GM4AJK/gps-staff/firmware/Nucleo-F767ZI/openspec/changes/bno085-int-edge-flag/specs/bno085-spi-bringup/spec.md

## MODIFIED Requirements

### Requirement: Wait for data-ready and read SHTP packet
`bno085_bringup()` SHALL pulse `RST` low for `BNO085_RESET_PULSE_MS` then
high twice in succession, waiting `BNO085_STARTUP_T1_MS` after each pulse
before doing anything else - per datasheet 6.5.3 "Startup timing", `INT` is
undefined for this period (`t1`, Internal Initialization) after `RST` is
released. A single reset pulse does not reliably bring the device up
following a power cycle; a second pulse is required.

After the second reset pulse and its `BNO085_STARTUP_T1_MS` wait,
`bno085_bringup()` SHALL wait (with a timeout of
`BNO085_INT_DEASSERT_TIMEOUT_MS`) for `INT` to read high (deasserted),
to allow the device's in-reset/booting period - during which it may
read or drive `INT` low for reasons unrelated to data-ready - to pass.
Immediately after this deassert wait (whether `INT` read high or the
deassert wait timed out), `bno085_bringup()` SHALL discard any
previously-latched `BNO085_INT` edge flag (`flag_get_BNO085_INT()`).
`bno085_bringup()` SHALL then wait for `INT` to become active, with a
timeout of `BNO085_INT_TIMEOUT_MS`. `INT` is considered active as soon
as either the `BNO085_INT` edge flag is set (a falling edge was latched
by `HAL_GPIO_EXTI_Callback()` at any point since it was discarded) or
the `INT` GPIO pin currently reads low - whichever is observed first. If
`INT` becomes active within the timeout, the driver SHALL assert `CS`
low, perform a single `BNO085_BRINGUP_BUF_SIZE`-byte full-duplex SPI
transfer (transmitting all-zero bytes), then release `CS` high. The
driver SHALL parse the first 4 received bytes as the SHTP header: a
16-bit length (LSB first, with the continuation bit masked off) into
`shtp_length`, followed by one byte each into `shtp_channel` and
`shtp_sequence`. The full received buffer SHALL be stored in the
handle.

#### Scenario: Two reset pulses are issued before waiting for data-ready
- **WHEN** `bno085_bringup()` is called
- **THEN** `RST` is pulsed low for `BNO085_RESET_PULSE_MS` then high, the
  driver waits `BNO085_STARTUP_T1_MS` without sampling `INT`, and this
  is repeated a second time before any `INT` polling begins

#### Scenario: Successful read populates the handle and returns HAL_OK
- **WHEN** `bno085_bringup()` is called, `INT` becomes active (edge
  latched or level low) within `BNO085_INT_TIMEOUT_MS` of the second
  `RST` release, and the SPI transfer succeeds
- **THEN** `bno085_bringup()` returns `HAL_OK`
- **AND** the handle's `shtp_length`, `shtp_channel`, and `shtp_sequence`
  fields reflect the first 4 bytes received
- **AND** the handle's raw receive buffer contains all
  `BNO085_BRINGUP_BUF_SIZE` bytes received over SPI

#### Scenario: A falling edge latched before the level-poll loop starts is not missed
- **WHEN** `bno085_bringup()` is called, the deassert wait completes (or
  times out), the `BNO085_INT` edge flag is discarded, `INT` briefly
  pulses low and back high (latching the flag via
  `HAL_GPIO_EXTI_Callback()`) before the level-poll loop begins, and the
  SPI transfer succeeds
- **THEN** `bno085_bringup()` returns `HAL_OK` without waiting for
  `BNO085_INT_TIMEOUT_MS`

#### Scenario: An edge latched during the in-reset/booting period is not mistaken for data-ready
- **WHEN** `bno085_bringup()` is called and `INT` reads/pulses low only
  during the `RST` pulse or the deassert wait (before the `BNO085_INT`
  edge flag is discarded), and then reads high for the remainder of the
  deassert wait
- **THEN** the latched edge from that period is discarded and does not
  cause `bno085_wait_int_low()` to return immediately
- **AND** `bno085_bringup()` waits for a genuine post-boot assertion of
  `INT` (edge or level) before performing the SPI transfer

#### Scenario: INT timeout returns an error without an SPI transaction
- **WHEN** `bno085_bringup()` is called and `INT` does not become active
  (no edge latched after the discard, and the level never reads low)
  within `BNO085_INT_TIMEOUT_MS` after the deassert wait completes
- **THEN** `bno085_bringup()` returns `HAL_TIMEOUT`
- **AND** no SPI transfer is performed
- **AND** `CS` remains high (deasserted)

#### Scenario: SPI failure during the read is propagated
- **WHEN** `INT` becomes active within the timeout, but the
  `HAL_SPI_TransmitReceive()` call fails (error or timeout)
- **THEN** `bno085_bringup()` returns the corresponding non-`HAL_OK`
  `HAL_StatusTypeDef`
- **AND** `CS` is released high (deasserted) before returning
