GM4AJK/gps-staff/firmware/Nucleo-F767ZI/openspec/changes/archive/2026-06-10-bno085-get-feature-enum/design.md

## Context

So far the driver only performs SPI *reads* triggered by `INT` going
low (`bno085_bringup()`, `bno085_read_advertisement()`). The SH-2
protocol's "Get Feature Request" (report ID `0xFE`) is sent *to* the
device on the SHTP control channel; the device replies with "Get
Feature Response" (`0xFC`) on the same channel once `INT` goes low.

From the bench-confirmed advertisement:
- channel 2 is `sensorhub:control` - the SH-2 command/control channel
- channel 3 is `sensorhub:inputNormal` - where unsolicited sensor
  reports normally arrive
- the advertisement's `tag 129` table lists `(report_id, max_length)`
  pairs for every report the firmware supports, including `01 0A`
  (Accelerometer), `02 0A` (Gyroscope), `03 0A` (Magnetic Field), `05
  0E` (Rotation Vector), `08 0C` (Game Rotation Vector), confirming
  these report IDs are valid to query

Each SHTP channel has an independent sequence number per direction
(host->device and device->host), starting at 0 and incrementing (with
wraparound) for each packet sent in that direction on that channel.
Until now the driver has only ever read on channel 0 (using whatever
sequence number the device sent), so it has never needed to track its
own outgoing sequence numbers.

## Goals / Non-Goals

**Goals:**
- Add a generic SPI write path (`bno085_send_packet()`) for sending an
  SHTP packet to a given channel, with the driver tracking its own
  per-channel TX sequence numbers.
- Implement `bno085_get_feature()`: send a Get Feature Request for a
  given SH-2 report ID on the control channel, wait for `INT`, read
  and parse the Get Feature Response.
- Demo: query a fixed list of well-known sensor report IDs
  (Accelerometer `0x01`, Gyroscope `0x02`, Magnetic Field `0x03`,
  Rotation Vector `0x05`, Game Rotation Vector `0x08`) and print each
  response over USART3.

**Non-Goals:**
- No Get Feature *Set* (enabling/configuring a sensor's report
  interval) - this change only queries current configuration.
- No dynamic enumeration from the advertisement's `tag 129` table -
  the demo uses a fixed, hand-picked list of report IDs known from the
  bench-captured advertisement. Driving the query list from a parsed
  `tag 129` table is a possible follow-up.
- No handling of unsolicited reports that may arrive on
  `inputNormal`/other channels interleaved with control-channel
  responses (see Risks).

## Decisions

- **`bno085_send_packet()` signature**: takes the handle, a channel
  number, a pointer to payload bytes, and a payload length. It builds
  the 4-byte SHTP header (length = 4 + payload length, channel, current
  TX sequence number for that channel), asserts `CS`, then performs a
  single full-duplex transfer of exactly `4 + payload length` bytes,
  capturing the received bytes into `cmd_buf`/`cmd_len` for debugging
  visibility (see "Full-duplex read-ahead" below), releases `CS`, and
  increments the channel's TX sequence number.
- **Exact-length two-step reads (header then payload)**: bench testing
  with a `cmd_buf` debug dump showed that `bno085_get_feature()` was
  reading a *previous* request's Get Feature Response shifted by one
  query (e.g. the Gyroscope query's `cmd_buf` contained the
  Accelerometer's response). Root cause: `bno085_read_advertisement()`
  always read the full `BNO085_ADVERT_BUF_SIZE` (320) bytes regardless
  of the advertisement's actual 276-byte length, over-reading by 44
  bytes into whatever the device queued next and leaving every
  subsequent read misaligned. Both `bno085_read_advertisement()` and
  `bno085_get_feature()`'s response read now read the 4-byte SHTP
  header first, then read exactly `length - 4` more bytes - never more,
  never fewer - so the device's queue stays aligned for the next read.
  This modifies the previously-archived `bno085-shtp-advertisement`
  capability (see its delta spec in this change).
- **Drain/retry loop in `bno085_get_feature()`**: bench testing showed
  that, even with exact-length reads, the response to a Get Feature
  Request is not always the next packet read - a previously-queued
  packet may be read first. `bno085_get_feature()` reads up to
  `BNO085_GET_FEATURE_MAX_ATTEMPTS` packets (via
  `bno085_read_response()`), discarding any that aren't a matching
  `0xFC`/`report_id` response, before giving up with `HAL_ERROR`.
- **`INT` wait before reads only, not writes**: an earlier iteration
  had `bno085_send_packet()` wait for `INT` low before every send, on
  the assumption that the device asserts `INT` before *any* SPI
  transaction. Bench testing showed this breaks every query after the
  first: once the device's queue is drained, `INT` stays deasserted and
  `bno085_send_packet()` times out (`HAL_TIMEOUT`) before the request is
  even transmitted. `bno085_send_packet()` no longer waits for `INT`;
  only `bno085_get_feature()`'s reads (via `bno085_read_response()`)
  wait for `INT` low.
- **Full-duplex read-ahead capture in `bno085_send_packet()`** (debug
  visibility only): SPI is full-duplex - every byte the host clocks out
  to send a request simultaneously shifts in a byte from the device.
  The previous implementation discarded these received bytes into a
  local, unused buffer. `bno085_send_packet()` now captures the
  `4 + payload length` bytes received during its transfer into
  `cmd_buf`/`cmd_len` so they're visible on the bench, but does not
  extend the transfer to cover a longer pending packet the device
  reports - an earlier iteration that did so (clocking extra
  zero-padded bytes into the device beyond our own packet) is suspected
  of leaving the device unresponsive to all subsequent commands.
  `bno085_get_feature()` always performs its own
  `bno085_read_response()` reads rather than relying on this captured
  data.
- **Per-channel TX sequence numbers**: add `uint8_t tx_seq[6]` to
  `bno085_t` (one counter per SHTP channel 0-5, matching the channels
  seen in the advertisement), initialized to 0 by `bno085_init()`
  (already zeroed via `memset`).
- **Command buffer**: add `uint8_t cmd_buf[BNO085_CMD_BUF_SIZE]` and
  `uint16_t cmd_len` with `BNO085_CMD_BUF_SIZE = 32` (Get Feature
  Response is 4-byte header + 17-byte payload = 21 bytes, so 32 gives
  margin), separate from `rx_buf`/`advert_buf` to keep each function's
  buffer purpose explicit, matching the pattern established for
  `advert_buf`. `cmd_len` records how many bytes of `cmd_buf` are valid
  (the received SHTP packet's declared length, capped to
  `BNO085_CMD_BUF_SIZE`), set by both `bno085_send_packet()` and
  `bno085_read_response()`.
- **`bno085_get_feature()` flow**:
  1. Build a 6-byte Get Feature Request payload: `{0xFE, report_id, 0,
     0, 0, 0}`.
  2. `bno085_send_packet()` on `BNO085_CHANNEL_CONTROL` (= 2).
  3. Wait for `INT` low with `BNO085_INT_TIMEOUT_MS` timeout (same
     pattern as `bno085_reset_and_wait()`'s poll loop, but without the
     `RST` pulse or deassert-debounce - those are reset-specific).
  4. On `INT` low, assert `CS`, `HAL_SPI_TransmitReceive()`
     `BNO085_CMD_BUF_SIZE` bytes into `cmd_buf`, release `CS`.
  5. Parse the SHTP header (bytes 0-3) and, if `cmd_buf[4] == 0xFC`
     (Get Feature Response) and `cmd_buf[5] == report_id`, parse the
     remaining 15 bytes into `bno085_feature_t` and return `HAL_OK`.
     Otherwise return a new sentinel status (see below).
- **`bno085_feature_t` struct fields** (from the Get Feature Response
  payload, all multi-byte fields little-endian): `feature_report_id`
  (`uint8_t`), `feature_flags` (`uint8_t`), `change_sensitivity`
  (`uint16_t`), `report_interval_us` (`uint32_t`), `batch_interval_us`
  (`uint32_t`), `sensor_specific_config` (`uint32_t`). A sensor is
  considered enabled if `report_interval_us != 0`.
- **Mismatch/unexpected response handling**: if the read packet's
  channel isn't `BNO085_CHANNEL_CONTROL`, or `cmd_buf[4]` isn't `0xFC`,
  or `cmd_buf[5]` doesn't match the requested `report_id`,
  `bno085_get_feature()` returns `HAL_ERROR` (the existing
  `HAL_StatusTypeDef` vocabulary already used for SPI failures, with
  `HAL_TIMEOUT` reserved for the `INT` wait). The raw `cmd_buf` remains
  available on the handle for inspection/debugging via USART3 in the
  demo.

- **PS0/WAKE pin added for waking the device before reads/writes**: bench
  testing of the drain/retry loop above showed that only the very first
  `bno085_get_feature()` call (Accelerometer, immediately after reset)
  ever received a response - every subsequent call (Gyroscope onward)
  timed out (`HAL_TIMEOUT`) waiting for `INT`, which never asserted
  again. The BNO08x datasheet states that pin 6 (PS0/WAKE) "must be
  connected to a GPIO so that the WAKE functionality can be performed":
  after reset, pulling PS0/WAKE low asks the device to assert `INT` (it
  asserts `INT` on its own only for its initial post-reset packet burst,
  then goes idle). The bench board's PS0/WAKE was originally hardwired
  high (tied for SPI mode select at reset, per the datasheet's "must be
  high from before reset until after the first assertion of `INT`"
  requirement), with no way to pulse it afterwards - hence the timeouts.
  The board was reworked to route PS0/WAKE to a spare GPIO
  (`BNO085_PS0_WAKE_Pin` = PF14, push-pull output, initially high to
  satisfy the reset-time mode-select requirement). A new helper,
  `bno085_wake_and_wait_int_low()`, is called at the start of both
  `bno085_send_packet()` and `bno085_read_response()`: if `INT` is
  already low it returns immediately, otherwise it pulses PS0/WAKE low,
  waits for `INT` low (`bno085_wait_int_low()`,
  `BNO085_INT_TIMEOUT_MS`), then returns PS0/WAKE high. This supersedes
  the "`INT` wait before reads only, not writes" decision above:
  `bno085_send_packet()` now also waits for `INT` (via the wake helper),
  but does so by actively requesting it rather than passively polling,
  so it no longer times out once the device's queue is drained.
  `bno085_reset_and_wait()` also explicitly drives PS0/WAKE high at its
  start, ahead of the `RST` pulse, to satisfy the reset-time
  requirement regardless of the pin's prior state.
- **Bench result**: with PS0/WAKE wired to PF14, all five queried
  sensors (Accelerometer, Gyroscope, Magnetic Field, Rotation Vector,
  Game Rotation Vector) return a correctly-framed Get Feature Response
  (`cmd_len == 21`, `cmd_buf[4] == 0xFC`, `cmd_buf[5] == report_id`) on
  the first attempt. All report `report_interval_us == 0` (supported but
  not yet enabled via Set Feature, which is out of scope for this
  change) - the fix is confirmed by the response framing/matching, not
  by a non-zero interval.

## Risks / Trade-offs

- [An unsolicited report (e.g. on `inputNormal`) could arrive and
  assert `INT` before/instead of the Get Feature Response] →
  `bno085_get_feature()` only performs a single read attempt per call
  and returns `HAL_ERROR` on a mismatched response; the demo prints the
  raw `cmd_buf` on mismatch so this is visible on the bench. A
  retry/loop could be added in a follow-up if this proves common in
  practice.
- [Sequence number tracking is host-side only and unvalidated against
  the device's expectations] → if the device rejects packets with
  unexpected sequence numbers, the first Get Feature Request (sequence
  0 on channel 2) should still work since both sides start at 0 after
  reset; this is the primary scenario exercised by the demo.
- [`BNO085_CMD_BUF_SIZE = 32` assumes Get Feature Response (21 bytes)
  is the largest control-channel response queried] → sufficient for
  this change's fixed report-ID list; a larger response would be
  truncated, visible as a short/garbled `cmd_buf` dump.
