GM4AJK/gps-staff/docs/reference/psu/sample_pcb.png

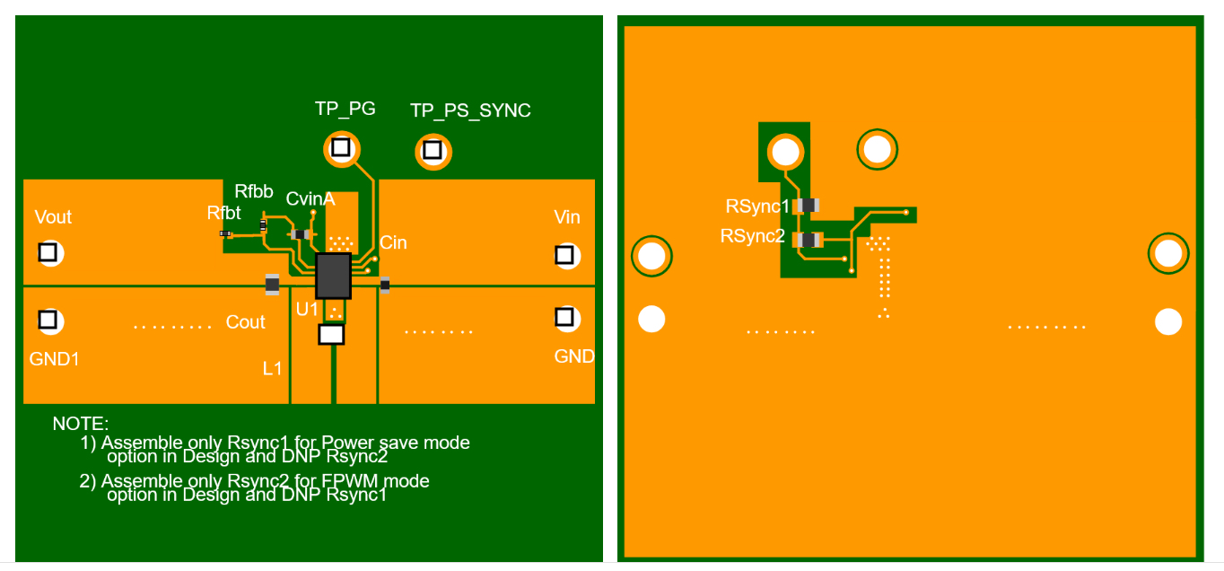
docs/reference/psu/sample_pcb.png
