GM4AJK/gps-staff/docs/reference/psu/sample_sch.png

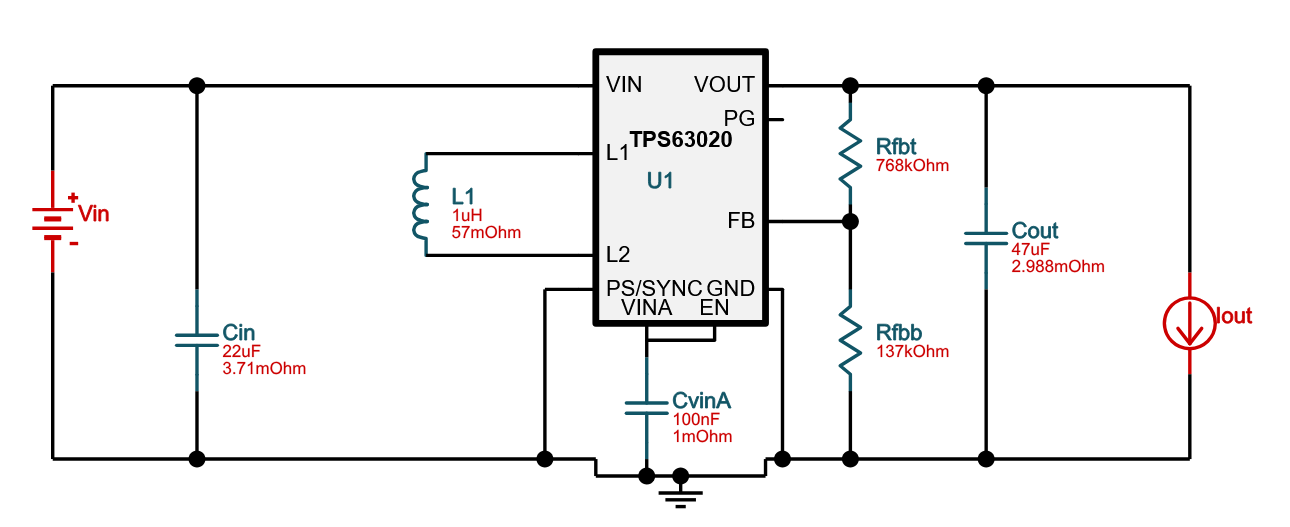
docs/reference/psu/sample_sch.png
