GM4AJK/gps-staff/firmware/Nucleo-F767ZI-FreeRTOS/Core/Inc/main.h

#define SX1262_SPI_BUSY_Pin GPIO_PIN_0
#define SX1262_SPI_BUSY_GPIO_Port GPIOC
#define SX1262_SPI_MISO_Pin GPIO_PIN_2
#define SX1262_SPI_MISO_GPIO_Port GPIOC
#define F9P_TX_Pin GPIO_PIN_2
#define F9P_TX_GPIO_Port GPIOA
#define F9P_RX_Pin GPIO_PIN_3
#define F9P_RX_GPIO_Port GPIOA
#define LD1_Pin GPIO_PIN_0
#define LD1_GPIO_Port GPIOB
#define STLK_RX_Pin GPIO_PIN_10
#define STLK_RX_GPIO_Port GPIOB
#define SX1262_SPI_RESET_Pin GPIO_PIN_11
#define SX1262_SPI_RESET_GPIO_Port GPIOB
#define SX1262_SPI_CS_Pin GPIO_PIN_12
#define SX1262_SPI_CS_GPIO_Port GPIOB
#define SX1262_SPI_SCLK_Pin GPIO_PIN_13
#define SX1262_SPI_SCLK_GPIO_Port GPIOB
#define LD3_Pin GPIO_PIN_14
#define LD3_GPIO_Port GPIOB
#define SX1262_SPI_MOSI_Pin GPIO_PIN_15
#define SX1262_SPI_MOSI_GPIO_Port GPIOB
#define STLK_TX_Pin GPIO_PIN_9
#define STLK_TX_GPIO_Port GPIOD
#define ILI9341_DC_Pin GPIO_PIN_2
#define ILI9341_DC_GPIO_Port GPIOG
#define ILI9341_Lite_Pin GPIO_PIN_3
#define ILI9341_Lite_GPIO_Port GPIOG
#define USB_PowerSwitchOn_Pin GPIO_PIN_6
#define USB_PowerSwitchOn_GPIO_Port GPIOG
#define USB_OverCurrent_Pin GPIO_PIN_7
#define USB_OverCurrent_GPIO_Port GPIOG
#define SX1262_SPI_TXEN_Pin GPIO_PIN_6
#define SX1262_SPI_TXEN_GPIO_Port GPIOC
#define SX1262_SPI_RXEN_Pin GPIO_PIN_7
#define SX1262_SPI_RXEN_GPIO_Port GPIOC
#define SX1262_SPI_DIO2_Pin GPIO_PIN_8
#define SX1262_SPI_DIO2_GPIO_Port GPIOC
#define SX1262_SPI_DIO1_Pin GPIO_PIN_9
#define SX1262_SPI_DIO1_GPIO_Port GPIOC
#define SX1262_SPI_DIO1_EXTI_IRQn EXTI9_5_IRQn
#define USB_SOF_Pin GPIO_PIN_8
#define USB_SOF_GPIO_Port GPIOA
#define USB_VBUS_Pin GPIO_PIN_9
#define USB_VBUS_GPIO_Port GPIOA
#define USB_ID_Pin GPIO_PIN_10
#define USB_ID_GPIO_Port GPIOA
#define USB_DM_Pin GPIO_PIN_11
#define USB_DM_GPIO_Port GPIOA
#define USB_DP_Pin GPIO_PIN_12
#define USB_DP_GPIO_Port GPIOA
#define TMS_Pin GPIO_PIN_13
#define TMS_GPIO_Port GPIOA
#define TCK_Pin GPIO_PIN_14
#define TCK_GPIO_Port GPIOA
#define ILI9341_SCK_Pin GPIO_PIN_10
#define ILI9341_SCK_GPIO_Port GPIOC
#define ILI9341_MISO_Pin GPIO_PIN_11
#define ILI9341_MISO_GPIO_Port GPIOC
#define ILI9341_MOSI_Pin GPIO_PIN_12
#define ILI9341_MOSI_GPIO_Port GPIOC
#define ILI9341_CS_Pin GPIO_PIN_2
#define ILI9341_CS_GPIO_Port GPIOD
#define SDMMC2_CK_Pin GPIO_PIN_6
#define SDMMC2_CK_GPIO_Port GPIOD
#define SDMMC2_CMD_Pin GPIO_PIN_7
#define SDMMC2_CMD_GPIO_Port GPIOD
#define SDMMC2_D0_Pin GPIO_PIN_9
#define SDMMC2_D0_GPIO_Port GPIOG
#define SCMMC_CD_Pin GPIO_PIN_13
#define SCMMC_CD_GPIO_Port GPIOG
#define SWO_Pin GPIO_PIN_3
#define SWO_GPIO_Port GPIOB
#define ILI9341_RST_Pin GPIO_PIN_4
#define ILI9341_RST_GPIO_Port GPIOB
#define LD2_Pin GPIO_PIN_7
#define LD2_GPIO_Port GPIOB
