GM4AJK/gps-staff/firmware/Nucleo-F446RE/Core/Src/ssd130x.c

#include "ssd130x.h"
#include <math.h>
#include <stdlib.h>
#include <string.h>

/* I2C control bytes (SSD1306/SSD1309 datasheet section 8.1.5) */
#define SSD130X_I2C_CONTROL_CMD  0x00
#define SSD130X_I2C_CONTROL_DATA 0x40
#define SSD130X_I2C_TIMEOUT_MS   100

/* Fundamental command set */
#define SSD130X_CMD_DISPLAY_OFF           0xAE
#define SSD130X_CMD_DISPLAY_ON            0xAF
#define SSD130X_CMD_SET_CLOCK_DIV         0xD5
#define SSD130X_CMD_SET_MULTIPLEX         0xA8
#define SSD130X_CMD_SET_DISPLAY_OFFSET    0xD3
#define SSD130X_CMD_SET_START_LINE        0x40
#define SSD130X_CMD_SEGMENT_REMAP         0xA1	/* columns mirrored (normal mount) */
#define SSD130X_CMD_SEGMENT_REMAP_NORMAL  0xA0	/* columns not mirrored (rotated 180°) */
#define SSD130X_CMD_COM_SCAN_DEC          0xC8	/* rows bottom-to-top (normal mount) */
#define SSD130X_CMD_COM_SCAN_INC          0xC0	/* rows top-to-bottom (rotated 180°) */
#define SSD130X_CMD_SET_COM_PINS          0xDA
#define SSD130X_CMD_SET_CONTRAST          0x81
#define SSD130X_CMD_SET_PRECHARGE         0xD9
#define SSD130X_CMD_SET_VCOMH             0xDB
#define SSD130X_CMD_ENTIRE_DISPLAY_RESUME 0xA4
#define SSD130X_CMD_NORMAL_DISPLAY        0xA6
#define SSD130X_CMD_DEACTIVATE_SCROLL     0x2E

/* SSD1306-only: internal charge pump */
#define SSD1306_CMD_CHARGE_PUMP           0x8D
#define SSD1306_CHARGE_PUMP_ON            0x14

/* Addressing */
#define SSD130X_CMD_SET_MEMORY_ADDR_MODE  0x20
#define SSD130X_MEMORY_ADDR_MODE_PAGE     0x02
#define SSD130X_CMD_SET_PAGE_START        0xB0
#define SSD130X_CMD_SET_LOW_COLUMN        0x00
#define SSD130X_CMD_SET_HIGH_COLUMN       0x10

/* Built-in 5x7 font glyphs, printable ASCII 0x20-0x7E. One byte per glyph
 * column (5 columns/glyph), bit 0 = top row. */
static const uint8_t font5x7_glyphs[95][5] = {
	{ 0x00, 0x00, 0x00, 0x00, 0x00 }, /* 0x20 ' ' */
	{ 0x00, 0x00, 0x5F, 0x00, 0x00 }, /* 0x21 '!' */
	{ 0x00, 0x03, 0x00, 0x03, 0x00 }, /* 0x22 '"' */
	{ 0x14, 0x7F, 0x14, 0x7F, 0x14 }, /* 0x23 '#' */
	{ 0x24, 0x2A, 0x7F, 0x2A, 0x12 }, /* 0x24 '$' */
	{ 0x43, 0x33, 0x08, 0x66, 0x61 }, /* 0x25 '%' */
	{ 0x36, 0x49, 0x55, 0x22, 0x50 }, /* 0x26 '&' */
	{ 0x00, 0x00, 0x03, 0x00, 0x00 }, /* 0x27 ''' */
	{ 0x00, 0x1C, 0x22, 0x41, 0x00 }, /* 0x28 '(' */
	{ 0x00, 0x41, 0x22, 0x1C, 0x00 }, /* 0x29 ')' */
	{ 0x14, 0x08, 0x3E, 0x08, 0x14 }, /* 0x2A '*' */
	{ 0x08, 0x08, 0x3E, 0x08, 0x08 }, /* 0x2B '+' */
	{ 0x00, 0x40, 0x20, 0x00, 0x00 }, /* 0x2C ',' */
	{ 0x08, 0x08, 0x08, 0x08, 0x08 }, /* 0x2D '-' */
	{ 0x00, 0x60, 0x60, 0x00, 0x00 }, /* 0x2E '.' */
	{ 0x40, 0x30, 0x08, 0x06, 0x01 }, /* 0x2F '/' */
	{ 0x3E, 0x51, 0x49, 0x45, 0x3E }, /* 0x30 '0' */
	{ 0x00, 0x42, 0x7F, 0x40, 0x00 }, /* 0x31 '1' */
	{ 0x42, 0x61, 0x51, 0x49, 0x46 }, /* 0x32 '2' */
	{ 0x22, 0x41, 0x49, 0x49, 0x36 }, /* 0x33 '3' */
	{ 0x18, 0x14, 0x12, 0x7F, 0x10 }, /* 0x34 '4' */
	{ 0x27, 0x45, 0x45, 0x45, 0x39 }, /* 0x35 '5' */
	{ 0x3C, 0x4A, 0x49, 0x49, 0x30 }, /* 0x36 '6' */
	{ 0x01, 0x71, 0x09, 0x05, 0x03 }, /* 0x37 '7' */
	{ 0x36, 0x49, 0x49, 0x49, 0x36 }, /* 0x38 '8' */
	{ 0x06, 0x49, 0x49, 0x29, 0x1E }, /* 0x39 '9' */
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
};

const ssd130x_font_t ssd130x_font8x8 = {
	.glyphs = &font8x8_glyphs[0][0],
	.glyph_width = 8,
	.glyph_height = 8,
	.advance = 9,
	.first_char = 0x20,
	.last_char = 0x7E,
};

const ssd130x_font_t ssd130x_font5x7 = {
	.glyphs = &font5x7_glyphs[0][0],
	.glyph_width = 5,
	.glyph_height = 7,
	.advance = 6,
	.first_char = 0x20,
	.last_char = 0x7E,
};

const ssd130x_font_t ssd130x_font10x14 = {
	.glyphs = &font10x14_glyphs[0][0],
	.glyph_width = 10,
	.glyph_height = 14,
	.advance = 12,
	.first_char = 0x20,
	.last_char = 0x7E,
};

static HAL_StatusTypeDef ssd130x_write_cmd(ssd130x_t *p, const uint8_t *cmds, uint16_t len)
{
	return HAL_I2C_Mem_Write(
		p->port,
		(uint16_t)(p->address << 1),
		SSD130X_I2C_CONTROL_CMD,
		I2C_MEMADD_SIZE_8BIT,
		(uint8_t *)cmds,
		len,
		SSD130X_I2C_TIMEOUT_MS
	);
}

static HAL_StatusTypeDef ssd130x_write_data(ssd130x_t *p, const uint8_t *data, uint16_t len)
{
	return HAL_I2C_Mem_Write(
		p->port,
		(uint16_t)(p->address << 1),
		SSD130X_I2C_CONTROL_DATA,
		I2C_MEMADD_SIZE_8BIT,
		(uint8_t *)data,
		len,
		SSD130X_I2C_TIMEOUT_MS
	);
}

static HAL_StatusTypeDef ssd130x_write_pages(ssd130x_t *p, const uint8_t *data)
{
	HAL_StatusTypeDef status;
	uint8_t num_pages = (uint8_t)(p->height / 8);

	for (uint8_t page = 0; page < num_pages; page++) {
		uint8_t page_cmds[] = {
			(uint8_t)(SSD130X_CMD_SET_PAGE_START + page),
			SSD130X_CMD_SET_LOW_COLUMN,
			SSD130X_CMD_SET_HIGH_COLUMN,
		};
		status = ssd130x_write_cmd(p, page_cmds, sizeof(page_cmds));
		if (status != HAL_OK) {
			return status;
		}

		status = ssd130x_write_data(p, &data[(uint16_t)page * p->width], (uint16_t)p->width);
		if (status != HAL_OK) {
			return status;
		}
	}

	return HAL_OK;
}

void ssd130x_init(
	ssd130x_t *p,
	I2C_HandleTypeDef *in_port,
	uint16_t in_address,
	ssd130x_chip_t chip,
	bool rotate_180,
	int16_t in_height,
	int16_t in_width)
{
	p->port = in_port;
	p->address = in_address;
	p->chip = chip;
	p->rotate_180 = rotate_180;
	p->height = (in_height < 0) ? 64 : in_height;
	p->width = (in_width < 0) ? 128 : in_width;
	memset(p->buffer, 0x00, sizeof(p->buffer));
	p->dirty = false;
}

HAL_StatusTypeDef ssd130x_bringup(ssd130x_t *p)
{
	HAL_StatusTypeDef status;

	uint8_t init_cmds[] = {
		SSD130X_CMD_DISPLAY_OFF,
		SSD130X_CMD_SET_CLOCK_DIV, 0x80,
		SSD130X_CMD_SET_MULTIPLEX, (uint8_t)(p->height - 1),
		SSD130X_CMD_SET_DISPLAY_OFFSET, 0x00,
		SSD130X_CMD_SET_START_LINE,
		p->rotate_180 ? SSD130X_CMD_SEGMENT_REMAP_NORMAL : SSD130X_CMD_SEGMENT_REMAP,
		p->rotate_180 ? SSD130X_CMD_COM_SCAN_INC        : SSD130X_CMD_COM_SCAN_DEC,
		SSD130X_CMD_SET_COM_PINS, 0x12,
		SSD130X_CMD_SET_CONTRAST, 0x8F,
		SSD130X_CMD_SET_PRECHARGE, 0xF1,
		SSD130X_CMD_SET_VCOMH, 0x40,
		SSD130X_CMD_ENTIRE_DISPLAY_RESUME,
		SSD130X_CMD_NORMAL_DISPLAY,
		SSD130X_CMD_DEACTIVATE_SCROLL,
	};

	status = ssd130x_write_cmd(p, init_cmds, sizeof(init_cmds));
	if (status != HAL_OK) {
		return status;
	}

	/* SSD1306 has an internal charge pump that must be enabled explicitly.
	 * SSD1309 uses an external charge pump circuit — this command is absent. */
	if (p->chip == SSD130X_CHIP_SSD1306) {
		uint8_t pump[] = { SSD1306_CMD_CHARGE_PUMP, SSD1306_CHARGE_PUMP_ON };
		status = ssd130x_write_cmd(p, pump, sizeof(pump));
		if (status != HAL_OK) {
			return status;
		}
	}

	uint8_t mem_addr_mode[] = {
		SSD130X_CMD_SET_MEMORY_ADDR_MODE, SSD130X_MEMORY_ADDR_MODE_PAGE,
	};
	status = ssd130x_write_cmd(p, mem_addr_mode, sizeof(mem_addr_mode));
	if (status != HAL_OK) {
		return status;
	}

	/* All-on test pattern, using the framebuffer as scratch space */
	size_t fb_size = (size_t)p->width * (size_t)(p->height / 8);
	memset(p->buffer, 0xFF, fb_size);
	status = ssd130x_write_pages(p, p->buffer);
	if (status != HAL_OK) {
		return status;
	}
	memset(p->buffer, 0x00, fb_size);
	p->dirty = false;

	uint8_t display_on[] = { SSD130X_CMD_DISPLAY_ON };
	return ssd130x_write_cmd(p, display_on, sizeof(display_on));
}

void ssd130x_clear(ssd130x_t *p)
{
	size_t fb_size = (size_t)p->width * (size_t)(p->height / 8);
	memset(p->buffer, 0x00, fb_size);
	p->dirty = true;
}

void ssd130x_fill(ssd130x_t *p, uint8_t color)
{
	size_t fb_size = (size_t)p->width * (size_t)(p->height / 8);
	memset(p->buffer, (color == SSD130X_COLOR_ON) ? 0xFF : 0x00, fb_size);
	p->dirty = true;
}

void ssd130x_set_pixel(ssd130x_t *p, int16_t x, int16_t y, uint8_t color)
{
	if (x < 0 || x >= p->width || y < 0 || y >= p->height) {
		return;
	}

	uint16_t index = (uint16_t)((y / 8) * p->width + x);
	uint8_t mask = (uint8_t)(1u << (y % 8));
	uint8_t old = p->buffer[index] & mask;
	uint8_t new = (color == SSD130X_COLOR_ON) ? mask : 0;

	if (old != new) {
		p->buffer[index] = (uint8_t)((p->buffer[index] & ~mask) | new);
		p->dirty = true;
	}
}

uint8_t ssd130x_get_pixel(ssd130x_t *p, int16_t x, int16_t y)
{
	if (x < 0 || x >= p->width || y < 0 || y >= p->height) {
		return SSD130X_COLOR_OFF;
	}

	uint16_t index = (uint16_t)((y / 8) * p->width + x);
	uint8_t mask = (uint8_t)(1u << (y % 8));

	return (p->buffer[index] & mask) ? SSD130X_COLOR_ON : SSD130X_COLOR_OFF;
}

HAL_StatusTypeDef ssd130x_flush(ssd130x_t *p)
{
	HAL_StatusTypeDef status;

	if (!p->dirty) {
		return HAL_OK;
	}

	status = ssd130x_write_pages(p, p->buffer);
	if (status == HAL_OK) {
		p->dirty = false;
	}

	return status;
}

void ssd130x_draw_line(ssd130x_t *p, int16_t x0, int16_t y0, int16_t x1, int16_t y1, uint8_t color)
{
	int16_t dx = (int16_t)abs(x1 - x0);
	int16_t dy = (int16_t)-abs(y1 - y0);
	int16_t sx = (x0 < x1) ? 1 : -1;
	int16_t sy = (y0 < y1) ? 1 : -1;
	int16_t err = (int16_t)(dx + dy);

	for (;;) {
		ssd130x_set_pixel(p, x0, y0, color);

		if (x0 == x1 && y0 == y1) {
			break;
		}

		int16_t e2 = (int16_t)(2 * err);
		if (e2 >= dy) {
			err = (int16_t)(err + dy);
			x0 = (int16_t)(x0 + sx);
		}
		if (e2 <= dx) {
			err = (int16_t)(err + dx);
			y0 = (int16_t)(y0 + sy);
		}
	}
}

void ssd130x_draw_rect(ssd130x_t *p, int16_t x0, int16_t y0, int16_t x1, int16_t y1, bool fill, uint8_t color)
{
	int16_t min_x = (x0 < x1) ? x0 : x1;
	int16_t max_x = (x0 < x1) ? x1 : x0;
	int16_t min_y = (y0 < y1) ? y0 : y1;
	int16_t max_y = (y0 < y1) ? y1 : y0;

	if (fill) {
		for (int16_t y = min_y; y <= max_y; y++) {
			for (int16_t x = min_x; x <= max_x; x++) {
				ssd130x_set_pixel(p, x, y, color);
			}
		}
	} else {
		ssd130x_draw_line(p, min_x, min_y, max_x, min_y, color);
		ssd130x_draw_line(p, min_x, max_y, max_x, max_y, color);
		ssd130x_draw_line(p, min_x, min_y, min_x, max_y, color);
		ssd130x_draw_line(p, max_x, min_y, max_x, max_y, color);
	}
}

void ssd130x_draw_circle(ssd130x_t *p, int16_t x0, int16_t y0, int16_t r, bool fill, uint8_t color)
{
	int16_t f = (int16_t)(1 - r);
	int16_t ddF_x = 1;
	int16_t ddF_y = (int16_t)(-2 * r);
	int16_t x = 0;
	int16_t y = r;

	if (fill) {
		ssd130x_draw_line(p, x0, (int16_t)(y0 - r), x0, (int16_t)(y0 + r), color);
		ssd130x_draw_line(p, (int16_t)(x0 - r), y0, (int16_t)(x0 + r), y0, color);
	} else {
		ssd130x_set_pixel(p, x0, (int16_t)(y0 + r), color);
		ssd130x_set_pixel(p, x0, (int16_t)(y0 - r), color);
		ssd130x_set_pixel(p, (int16_t)(x0 + r), y0, color);
		ssd130x_set_pixel(p, (int16_t)(x0 - r), y0, color);
	}

	while (x < y) {
		if (f >= 0) {
			y--;
			ddF_y = (int16_t)(ddF_y + 2);
			f = (int16_t)(f + ddF_y);
		}
		x++;
		ddF_x = (int16_t)(ddF_x + 2);
		f = (int16_t)(f + ddF_x);

		if (fill) {
			ssd130x_draw_line(p, (int16_t)(x0 - x), (int16_t)(y0 + y), (int16_t)(x0 + x), (int16_t)(y0 + y), color);
			ssd130x_draw_line(p, (int16_t)(x0 - x), (int16_t)(y0 - y), (int16_t)(x0 + x), (int16_t)(y0 - y), color);
			ssd130x_draw_line(p, (int16_t)(x0 - y), (int16_t)(y0 + x), (int16_t)(x0 + y), (int16_t)(y0 + x), color);
			ssd130x_draw_line(p, (int16_t)(x0 - y), (int16_t)(y0 - x), (int16_t)(x0 + y), (int16_t)(y0 - x), color);
		} else {
			ssd130x_set_pixel(p, (int16_t)(x0 + x), (int16_t)(y0 + y), color);
			ssd130x_set_pixel(p, (int16_t)(x0 - x), (int16_t)(y0 + y), color);
			ssd130x_set_pixel(p, (int16_t)(x0 + x), (int16_t)(y0 - y), color);
			ssd130x_set_pixel(p, (int16_t)(x0 - x), (int16_t)(y0 - y), color);
			ssd130x_set_pixel(p, (int16_t)(x0 + y), (int16_t)(y0 + x), color);
			ssd130x_set_pixel(p, (int16_t)(x0 - y), (int16_t)(y0 + x), color);
			ssd130x_set_pixel(p, (int16_t)(x0 + y), (int16_t)(y0 - x), color);
			ssd130x_set_pixel(p, (int16_t)(x0 - y), (int16_t)(y0 - x), color);
		}
	}
}

void ssd130x_draw_arrow(ssd130x_t *p, int16_t x0, int16_t y0, int16_t x1, int16_t y1, int16_t size, uint8_t color)
{
	ssd130x_draw_line(p, x0, y0, x1, y1, color);

	if (size > 0) {
		float angle = atan2f((float)(y1 - y0), (float)(x1 - x0));
		float wing_angle = (float)M_PI / 6.0f;
		float length = (float)size + 2.0f;

		float wx0 = (float)x1 - length * cosf(angle - wing_angle);
		float wy0 = (float)y1 - length * sinf(angle - wing_angle);
		float wx1 = (float)x1 - length * cosf(angle + wing_angle);
		float wy1 = (float)y1 - length * sinf(angle + wing_angle);

		int16_t steps = (int16_t)(2 * size + 4);
		for (int16_t i = 0; i <= steps; i++) {
			float t = (float)i / (float)steps;
			int16_t bx = (int16_t)lrintf(wx0 + t * (wx1 - wx0));
			int16_t by = (int16_t)lrintf(wy0 + t * (wy1 - wy0));
			ssd130x_draw_line(p, x1, y1, bx, by, color);
		}
	}
}

void ssd130x_draw_triangle(ssd130x_t *p, int16_t x0, int16_t y0, int16_t x1, int16_t y1, int16_t x2, int16_t y2, bool fill, uint8_t color)
{
	if (!fill) {
		ssd130x_draw_line(p, x0, y0, x1, y1, color);
		ssd130x_draw_line(p, x1, y1, x2, y2, color);
		ssd130x_draw_line(p, x2, y2, x0, y0, color);
		return;
	}

	int16_t tmp;
	if (y0 > y1) { tmp = y0; y0 = y1; y1 = tmp; tmp = x0; x0 = x1; x1 = tmp; }
	if (y1 > y2) { tmp = y1; y1 = y2; y2 = tmp; tmp = x1; x1 = x2; x2 = tmp; }
	if (y0 > y1) { tmp = y0; y0 = y1; y1 = tmp; tmp = x0; x0 = x1; x1 = tmp; }

	if (y0 == y2) {
		int16_t min_x = x0, max_x = x0;
		if (x1 < min_x) min_x = x1; else if (x1 > max_x) max_x = x1;
		if (x2 < min_x) min_x = x2; else if (x2 > max_x) max_x = x2;
		ssd130x_draw_line(p, min_x, y0, max_x, y0, color);
		return;
	}

	int16_t dx01 = (int16_t)(x1 - x0), dy01 = (int16_t)(y1 - y0);
	int16_t dx02 = (int16_t)(x2 - x0), dy02 = (int16_t)(y2 - y0);
	int16_t dx12 = (int16_t)(x2 - x1), dy12 = (int16_t)(y2 - y1);
	int32_t sa = 0, sb = 0;
	int16_t y, last;

	last = (y1 == y2) ? y1 : (int16_t)(y1 - 1);
	for (y = y0; y <= last; y++) {
		int16_t a = (int16_t)(x0 + sa / dy01);
		int16_t b = (int16_t)(x0 + sb / dy02);
		sa = (int32_t)(sa + dx01);
		sb = (int32_t)(sb + dx02);
		if (a > b) { tmp = a; a = b; b = tmp; }
		ssd130x_draw_line(p, a, y, b, y, color);
	}

	sa = (int32_t)dx12 * (int32_t)(y - y1);
	sb = (int32_t)dx02 * (int32_t)(y - y0);
	for (; y <= y2; y++) {
		int16_t a = (int16_t)(x1 + sa / dy12);
		int16_t b = (int16_t)(x0 + sb / dy02);
		sa = (int32_t)(sa + dx12);
		sb = (int32_t)(sb + dx02);
		if (a > b) { tmp = a; a = b; b = tmp; }
		ssd130x_draw_line(p, a, y, b, y, color);
	}
}

void ssd130x_draw_polygon(ssd130x_t *p, const ssd130x_point_t *points, uint8_t num_points, bool fill, uint8_t color)
{
	if (num_points < 3) {
		return;
	}

	if (!fill) {
		for (uint8_t i = 0; i < num_points; i++) {
			const ssd130x_point_t *a = &points[i];
			const ssd130x_point_t *b = &points[(i + 1) % num_points];
			ssd130x_draw_line(p, a->x, a->y, b->x, b->y, color);
		}
		return;
	}

	int16_t min_y = points[0].y, max_y = points[0].y;
	for (uint8_t i = 1; i < num_points; i++) {
		if (points[i].y < min_y) min_y = points[i].y;
		if (points[i].y > max_y) max_y = points[i].y;
	}

	for (int16_t y = min_y; y <= max_y; y++) {
		int16_t nodes[SSD130X_POLYGON_MAX_POINTS];
		uint8_t node_count = 0;

		for (uint8_t i = 0; i < num_points; i++) {
			const ssd130x_point_t *a = &points[i];
			const ssd130x_point_t *b = &points[(i + 1) % num_points];

			if ((a->y <= y && b->y > y) || (b->y <= y && a->y > y)) {
				int32_t x = (int32_t)a->x + (int32_t)(y - a->y) * (int32_t)(b->x - a->x) / (int32_t)(b->y - a->y);
				if (node_count < SSD130X_POLYGON_MAX_POINTS) {
					nodes[node_count++] = (int16_t)x;
				}
			}
		}

		for (uint8_t i = 1; i < node_count; i++) {
			int16_t key = nodes[i];
			int8_t j = (int8_t)(i - 1);
			while (j >= 0 && nodes[j] > key) {
				nodes[j + 1] = nodes[j];
				j--;
			}
			nodes[j + 1] = key;
		}

		for (uint8_t i = 0; (uint8_t)(i + 1) < node_count; i = (uint8_t)(i + 2)) {
			ssd130x_draw_line(p, nodes[i], y, nodes[i + 1], y, color);
		}
	}
}

void ssd130x_draw_char(ssd130x_t *p, const ssd130x_font_t *font, int16_t x, int16_t y, char c, uint8_t color)
{
	if (c < font->first_char || c > font->last_char) {
		return;
	}

	uint8_t rows_per_chunk = (uint8_t)((font->glyph_height + 7) / 8);
	const uint8_t *glyph = &font->glyphs[(c - font->first_char) * font->glyph_width * rows_per_chunk];

	for (uint8_t col = 0; col < font->glyph_width; col++) {
		for (uint8_t chunk = 0; chunk < rows_per_chunk; chunk++) {
			uint8_t bits = glyph[col * rows_per_chunk + chunk];
			for (uint8_t bit = 0; bit < 8; bit++) {
				uint8_t row = (uint8_t)(chunk * 8 + bit);
				if (row >= font->glyph_height) {
					break;
				}
				if (bits & (1u << bit)) {
					ssd130x_set_pixel(p, (int16_t)(x + col), (int16_t)(y + row), color);
				}
			}
		}
	}
}

void ssd130x_draw_string(ssd130x_t *p, const ssd130x_font_t *font, int16_t x, int16_t y, const char *str, uint8_t color)
{
	while (*str != '\0') {
		ssd130x_draw_char(p, font, x, y, *str, color);
		x = (int16_t)(x + font->advance);
		str++;
	}
}
