GM4AJK/gps-staff/firmware/Nucleo-F767ZI-FreeRTOS/Core/Inc/ssd1309.h

#ifndef INC_SSD1309_H_
#define INC_SSD1309_H_

#include "main.h"
#include <stdint.h>
#include <stdbool.h>

/* Max framebuffer size: 128 cols x 8 pages (128x64 panel, 1bpp) */
#define SSD1309_FB_SIZE (128u * 64u / 8u)

#define SSD1309_COLOR_OFF 0
#define SSD1309_COLOR_ON  1

/* Max vertices supported by ssd1309_draw_polygon() */
#define SSD1309_POLYGON_MAX_POINTS 32

typedef struct {
	I2C_HandleTypeDef *port;
	uint16_t address;
	int16_t height;
	int16_t width;
	uint8_t buffer[SSD1309_FB_SIZE];
	bool dirty;
} ssd1309_t;

/**
 * ssd1309_point_t
 *
 * A single (x, y) vertex, used by ssd1309_draw_polygon().
 */
typedef struct {
	int16_t x;
	int16_t y;
} ssd1309_point_t;

/**
 * ssd1309_font_t
 *
 * Describes a fixed-width font. Glyphs cover the inclusive character range
 * `first_char`..`last_char` and are stored in `glyphs` column-major, with
 * `(glyph_height + 7) / 8` bytes per column (bit 0 = top row of each 8-row
 * chunk). `advance` is the x distance in pixels from one glyph's origin to
 * the next.
 */
typedef struct {
	const uint8_t *glyphs;
	uint8_t glyph_width;
	uint8_t glyph_height;
	uint8_t advance;
	char first_char;
	char last_char;
} ssd1309_font_t;

/* Built-in fonts, all covering printable ASCII 0x20-0x7E */
extern const ssd1309_font_t font5x7;
extern const ssd1309_font_t font8x8;
extern const ssd1309_font_t font10x14;


/**
 * ssd1309_init
 * @param p - Pointer to ssd1309_t struct
 * @param in_port - Pointer to I2C_HandleTypeDef
 * @param in_address - The 7-bit I2C address
 * @param in_height - The  display pixel height (-1 defaults to 64)
 * @param in_width - The  display pixel width (-1 defaults to 128)
 *
 * Populates the handle and clears the framebuffer - no I2C traffic is sent.
 */
void ssd1309_init(
	ssd1309_t *p,
	I2C_HandleTypeDef *in_port,
	uint16_t in_address,
	int16_t in_height,
	int16_t in_width
);

/**
 * ssd1309_bringup
 * @param p - Pointer to an initialized ssd1309_t struct
 *
 * Sends the SSD1309 power-on init command sequence followed by an
 * all-pixels-on test pattern, then turns the display on. Intended as a
 * bench bring-up / wiring smoke test.
 *
 * @return HAL_OK on success, or the HAL_StatusTypeDef of the first failed
 *         I2C transfer.
 */
HAL_StatusTypeDef ssd1309_bringup(ssd1309_t *p);

/**
 * ssd1309_clear
 * @param p - Pointer to ssd1309_t struct
 *
 * Sets every pixel in the framebuffer off and marks it dirty.
 */
void ssd1309_clear(ssd1309_t *p);

/**
 * ssd1309_fill
 * @param p - Pointer to ssd1309_t struct
 * @param color - SSD1309_COLOR_OFF or SSD1309_COLOR_ON
 *
 * Sets every pixel in the framebuffer to color and marks it dirty.
 */
void ssd1309_fill(ssd1309_t *p, uint8_t color);

/**
 * ssd1309_set_pixel
 * @param p - Pointer to ssd1309_t struct
 * @param x - Column (0 .. width-1)
 * @param y - Row (0 .. height-1)
 * @param color - SSD1309_COLOR_OFF or SSD1309_COLOR_ON
 *
 * Out-of-bounds coordinates are silently ignored. Marks the framebuffer
 * dirty only if the pixel's value actually changes.
 */
void ssd1309_set_pixel(ssd1309_t *p, int16_t x, int16_t y, uint8_t color);

/**
 * ssd1309_get_pixel
 * @param p - Pointer to ssd1309_t struct
 * @param x - Column (0 .. width-1)
 * @param y - Row (0 .. height-1)
 *
 * @return SSD1309_COLOR_ON or SSD1309_COLOR_OFF. Out-of-bounds coordinates
 *         return SSD1309_COLOR_OFF.
 */
uint8_t ssd1309_get_pixel(ssd1309_t *p, int16_t x, int16_t y);

/**
 * ssd1309_flush
 * @param p - Pointer to an initialized ssd1309_t struct, after a
 *            successful ssd1309_bringup()
 *
 * Writes the framebuffer to GDDRAM via page-addressing mode if the
 * framebuffer is dirty; otherwise a no-op.
 *
 * @return HAL_OK on success or if not dirty, or the HAL_StatusTypeDef of
 *         the first failed I2C transfer (dirty flag is left set).
 */
HAL_StatusTypeDef ssd1309_flush(ssd1309_t *p);

/**
 * ssd1309_draw_line
 * @param p - Pointer to ssd1309_t struct
 * @param x0 - Column of the first endpoint
 * @param y0 - Row of the first endpoint
 * @param x1 - Column of the second endpoint
 * @param y1 - Row of the second endpoint
 * @param color - SSD1309_COLOR_OFF or SSD1309_COLOR_ON
 *
 * Draws a 1px-wide line between (x0, y0) and (x1, y1) inclusive using
 * Bresenham's algorithm and ssd1309_set_pixel() (so out-of-bounds points
 * are clipped per ssd1309_set_pixel() semantics).
 */
void ssd1309_draw_line(ssd1309_t *p, int16_t x0, int16_t y0, int16_t x1, int16_t y1, uint8_t color);

/**
 * ssd1309_draw_rect
 * @param p - Pointer to ssd1309_t struct
 * @param x0 - Column of the first corner
 * @param y0 - Row of the first corner
 * @param x1 - Column of the opposite corner
 * @param y1 - Row of the opposite corner
 * @param fill - false: draw a 1px-wide outline only; true: fill the
 *               rectangle
 * @param color - SSD1309_COLOR_OFF or SSD1309_COLOR_ON
 *
 * Draws a rectangle with corners (x0, y0) and (x1, y1) inclusive, in any
 * corner order, using ssd1309_draw_line()/ssd1309_set_pixel() (so
 * out-of-bounds points are clipped per ssd1309_set_pixel() semantics).
 */
void ssd1309_draw_rect(ssd1309_t *p, int16_t x0, int16_t y0, int16_t x1, int16_t y1, bool fill, uint8_t color);

/**
 * ssd1309_draw_circle
 * @param p - Pointer to ssd1309_t struct
 * @param x0 - Column of the circle's center
 * @param y0 - Row of the circle's center
 * @param r - Radius in pixels (0 draws a single point)
 * @param fill - false: draw a 1px-wide outline only; true: fill the disc
 * @param color - SSD1309_COLOR_OFF or SSD1309_COLOR_ON
 *
 * Draws a circle centered at (x0, y0) with radius r using the midpoint
 * circle algorithm and ssd1309_set_pixel()/ssd1309_draw_line() (so
 * out-of-bounds points are clipped per ssd1309_set_pixel() semantics).
 */
void ssd1309_draw_circle(ssd1309_t *p, int16_t x0, int16_t y0, int16_t r, bool fill, uint8_t color);

/**
 * ssd1309_draw_polygon
 * @param p - Pointer to ssd1309_t struct
 * @param points - Array of vertices (closed automatically: an edge is
 *                  drawn/filled from points[num_points-1] back to
 *                  points[0])
 * @param num_points - Number of vertices in `points` (must be >= 3 and
 *                      <= SSD1309_POLYGON_MAX_POINTS; otherwise no-op for
 *                      < 3, and intersections beyond
 *                      SSD1309_POLYGON_MAX_POINTS per scanline are dropped
 *                      when filled)
 * @param fill - false: draw a 1px-wide outline only; true: fill the
 *               polygon using the even-odd scanline rule
 * @param color - SSD1309_COLOR_OFF or SSD1309_COLOR_ON
 *
 * Draws a closed polygon through points[0]..points[num_points-1], using
 * ssd1309_draw_line() (so out-of-bounds points are clipped per
 * ssd1309_set_pixel() semantics).
 */
void ssd1309_draw_polygon(ssd1309_t *p, const ssd1309_point_t *points, uint8_t num_points, bool fill, uint8_t color);

/**
 * ssd1309_draw_triangle
 * @param p - Pointer to ssd1309_t struct
 * @param x0 - Column of the first vertex
 * @param y0 - Row of the first vertex
 * @param x1 - Column of the second vertex
 * @param y1 - Row of the second vertex
 * @param x2 - Column of the third vertex
 * @param y2 - Row of the third vertex
 * @param fill - false: draw a 1px-wide outline only; true: fill the
 *               triangle
 * @param color - SSD1309_COLOR_OFF or SSD1309_COLOR_ON
 *
 * Draws a triangle with vertices (x0,y0), (x1,y1), (x2,y2), in any vertex
 * order, using ssd1309_draw_line()/ssd1309_set_pixel() (so out-of-bounds
 * points are clipped per ssd1309_set_pixel() semantics).
 */
void ssd1309_draw_triangle(ssd1309_t *p, int16_t x0, int16_t y0, int16_t x1, int16_t y1, int16_t x2, int16_t y2, bool fill, uint8_t color);

/**
 * ssd1309_draw_arrow
 * @param p - Pointer to ssd1309_t struct
 * @param x0 - Column of the shaft's start point
 * @param y0 - Row of the shaft's start point
 * @param x1 - Column of the shaft's end point (arrowhead tip)
 * @param y1 - Row of the shaft's end point (arrowhead tip)
 * @param size - Approximate pixel width of the arrowhead's base (the
 *               actual base width is approximately size + 2); <= 0 draws
 *               only the shaft
 * @param color - SSD1309_COLOR_OFF or SSD1309_COLOR_ON
 *
 * Draws a 1px-wide line from (x0, y0) to (x1, y1) via ssd1309_draw_line(),
 * plus (if size > 0) a filled triangular arrowhead at (x1, y1): two base
 * corners at approximately +/-30 degrees from the shaft's direction and
 * `size + 2` pixels from the tip, filled by fanning lines from the tip to
 * points along the base. Out-of-bounds points are clipped per
 * ssd1309_set_pixel() semantics.
 */
void ssd1309_draw_arrow(ssd1309_t *p, int16_t x0, int16_t y0, int16_t x1, int16_t y1, int16_t size, uint8_t color);

/**
 * ssd1309_draw_char
 * @param p - Pointer to ssd1309_t struct
 * @param font - Font to draw with (e.g. &font5x7, &font8x8, &font10x14)
 * @param x - Column of the glyph's top-left pixel
 * @param y - Row of the glyph's top-left pixel
 * @param c - Character to draw; values outside font->first_char..last_char
 *            render blank
 * @param color - SSD1309_COLOR_OFF or SSD1309_COLOR_ON
 *
 * Draws a glyph_width x glyph_height glyph from `font` using
 * ssd1309_set_pixel().
 */
void ssd1309_draw_char(ssd1309_t *p, const ssd1309_font_t *font, int16_t x, int16_t y, char c, uint8_t color);

/**
 * ssd1309_draw_string
 * @param p - Pointer to ssd1309_t struct
 * @param font - Font to draw with (e.g. &font5x7, &font8x8, &font10x14)
 * @param x - Column of the first glyph's top-left pixel
 * @param y - Row of the first glyph's top-left pixel
 * @param str - NUL-terminated string to draw
 * @param color - SSD1309_COLOR_OFF or SSD1309_COLOR_ON
 *
 * Draws each character via ssd1309_draw_char(), advancing x by
 * font->advance pixels per character. No wrapping is performed.
 */
void ssd1309_draw_string(ssd1309_t *p, const ssd1309_font_t *font, int16_t x, int16_t y, const char *str, uint8_t color);

#endif /* INC_SSD1309_H_ */
