GM4AJK/gps-staff/firmware/esp32-handheld/main/waveshare_rgb_lcd_port.c

/*
 * SPDX-FileCopyrightText: 2022 Espressif Systems (Shanghai) CO LTD
 * SPDX-License-Identifier: CC0-1.0
 */

#include "waveshare_rgb_lcd_port.h"

static const char *TAG = "handheld";

IRAM_ATTR static bool rgb_lcd_on_vsync_event(esp_lcd_panel_handle_t panel, const esp_lcd_rgb_panel_event_data_t *edata, void *user_ctx)
{
    return lvgl_port_notify_rgb_vsync();
}

#if CONFIG_EXAMPLE_LCD_TOUCH_CONTROLLER_GT911
static i2c_master_bus_handle_t i2c_bus_handle = NULL;

static esp_err_t i2c_master_init(void)
{
    i2c_master_bus_config_t bus_cfg = {
        .clk_source = I2C_CLK_SRC_DEFAULT,
        .i2c_port = I2C_MASTER_NUM,
        .scl_io_num = I2C_MASTER_SCL_IO,
        .sda_io_num = I2C_MASTER_SDA_IO,
        .glitch_ignore_cnt = 7,
        .flags.enable_internal_pullup = true,
    };
    return i2c_new_master_bus(&bus_cfg, &i2c_bus_handle);
}

static esp_err_t i2c_write_byte(uint8_t dev_addr, uint8_t val)
{
    i2c_device_config_t dev_cfg = {
        .dev_addr_length = I2C_ADDR_BIT_LEN_7,
        .device_address = dev_addr,
        .scl_speed_hz = I2C_MASTER_FREQ_HZ,
    };
    i2c_master_dev_handle_t dev_handle;
    esp_err_t ret = i2c_master_bus_add_device(i2c_bus_handle, &dev_cfg, &dev_handle);
    if (ret != ESP_OK) return ret;
    ret = i2c_master_transmit(dev_handle, &val, 1, I2C_MASTER_TIMEOUT_MS);
    i2c_master_bus_rm_device(dev_handle);
    return ret;
}

static void gpio_init(void)
{
    gpio_config_t io_conf = {
        .intr_type = GPIO_INTR_DISABLE,
        .pin_bit_mask = GPIO_INPUT_PIN_SEL,
        .mode = GPIO_MODE_OUTPUT,
    };
    gpio_config(&io_conf);
}

static void waveshare_esp32_s3_touch_reset(void)
{
    i2c_write_byte(0x24, 0x01);
    i2c_write_byte(0x38, 0x2C);
    esp_rom_delay_us(100 * 1000);
    gpio_set_level(GPIO_INPUT_IO_4, 0);
    esp_rom_delay_us(100 * 1000);
    i2c_write_byte(0x38, 0x2E);
    esp_rom_delay_us(200 * 1000);
}
#endif /* CONFIG_EXAMPLE_LCD_TOUCH_CONTROLLER_GT911 */

esp_err_t waveshare_esp32_s3_rgb_lcd_init(void)
{
    ESP_LOGI(TAG, "Install RGB LCD panel driver");
    esp_lcd_panel_handle_t panel_handle = NULL;
    esp_lcd_rgb_panel_config_t panel_config = {
        .clk_src = LCD_CLK_SRC_DEFAULT,
        .timings = {
            .pclk_hz = EXAMPLE_LCD_PIXEL_CLOCK_HZ,
            .h_res = EXAMPLE_LCD_H_RES,
            .v_res = EXAMPLE_LCD_V_RES,
            .hsync_pulse_width = 4,
            .hsync_back_porch = 8,
            .hsync_front_porch = 8,
            .vsync_pulse_width = 4,
            .vsync_back_porch = 8,
            .vsync_front_porch = 8,
            .flags = {
                .pclk_active_neg = 1,
            },
        },
        .data_width = EXAMPLE_RGB_DATA_WIDTH,
        .num_fbs = LVGL_PORT_LCD_RGB_BUFFER_NUMS,
        .bounce_buffer_size_px = EXAMPLE_RGB_BOUNCE_BUFFER_SIZE,
        .hsync_gpio_num = EXAMPLE_LCD_IO_RGB_HSYNC,
        .vsync_gpio_num = EXAMPLE_LCD_IO_RGB_VSYNC,
        .de_gpio_num = EXAMPLE_LCD_IO_RGB_DE,
        .pclk_gpio_num = EXAMPLE_LCD_IO_RGB_PCLK,
        .disp_gpio_num = EXAMPLE_LCD_IO_RGB_DISP,
        .data_gpio_nums = {
            EXAMPLE_LCD_IO_RGB_DATA0,
            EXAMPLE_LCD_IO_RGB_DATA1,
            EXAMPLE_LCD_IO_RGB_DATA2,
            EXAMPLE_LCD_IO_RGB_DATA3,
            EXAMPLE_LCD_IO_RGB_DATA4,
            EXAMPLE_LCD_IO_RGB_DATA5,
            EXAMPLE_LCD_IO_RGB_DATA6,
            EXAMPLE_LCD_IO_RGB_DATA7,
            EXAMPLE_LCD_IO_RGB_DATA8,
            EXAMPLE_LCD_IO_RGB_DATA9,
            EXAMPLE_LCD_IO_RGB_DATA10,
            EXAMPLE_LCD_IO_RGB_DATA11,
            EXAMPLE_LCD_IO_RGB_DATA12,
            EXAMPLE_LCD_IO_RGB_DATA13,
            EXAMPLE_LCD_IO_RGB_DATA14,
            EXAMPLE_LCD_IO_RGB_DATA15,
        },
        .flags = {
            .fb_in_psram = 1,
        },
    };

    ESP_ERROR_CHECK(esp_lcd_new_rgb_panel(&panel_config, &panel_handle));

    ESP_LOGI(TAG, "Initialize RGB LCD panel");
    ESP_ERROR_CHECK(esp_lcd_panel_init(panel_handle));

    esp_lcd_touch_handle_t tp_handle = NULL;
#if CONFIG_EXAMPLE_LCD_TOUCH_CONTROLLER_GT911
    ESP_LOGI(TAG, "Initialize I2C bus");
    ESP_ERROR_CHECK(i2c_master_init());
    ESP_LOGI(TAG, "Initialize GPIO");
    gpio_init();
    ESP_LOGI(TAG, "Initialize Touch LCD");
    waveshare_esp32_s3_touch_reset();

    esp_lcd_panel_io_handle_t tp_io_handle = NULL;
    const esp_lcd_panel_io_i2c_config_t tp_io_config = ESP_LCD_TOUCH_IO_I2C_GT911_CONFIG();
    ESP_ERROR_CHECK(esp_lcd_new_panel_io_i2c(i2c_bus_handle, &tp_io_config, &tp_io_handle));

    ESP_LOGI(TAG, "Initialize touch controller GT911");
    const esp_lcd_touch_config_t tp_cfg = {
        .x_max = EXAMPLE_LCD_H_RES,
        .y_max = EXAMPLE_LCD_V_RES,
        .rst_gpio_num = EXAMPLE_PIN_NUM_TOUCH_RST,
        .int_gpio_num = EXAMPLE_PIN_NUM_TOUCH_INT,
        .levels = { .reset = 0, .interrupt = 0 },
        .flags = { .swap_xy = 0, .mirror_x = 0, .mirror_y = 0 },
    };
    ESP_ERROR_CHECK(esp_lcd_touch_new_i2c_gt911(tp_io_handle, &tp_cfg, &tp_handle));
#endif

    ESP_ERROR_CHECK(lvgl_port_init(panel_handle, tp_handle));

    esp_lcd_rgb_panel_event_callbacks_t cbs = {
        .on_vsync = rgb_lcd_on_vsync_event,
    };
    ESP_ERROR_CHECK(esp_lcd_rgb_panel_register_event_callbacks(panel_handle, &cbs, NULL));

    return ESP_OK;
}

esp_err_t wavesahre_rgb_lcd_bl_on(void)
{
    i2c_write_byte(0x24, 0x01);
    i2c_write_byte(0x38, 0x1E);
    return ESP_OK;
}

esp_err_t wavesahre_rgb_lcd_bl_off(void)
{
    i2c_write_byte(0x24, 0x01);
    i2c_write_byte(0x38, 0x1A);
    return ESP_OK;
}
