GM4AJK/gps-staff/firmware/esp32-handheld/main/wifi_provision.h

#pragma once
#include "waveshare_rgb_lcd_port.h"
#include "ble_base_client.h"

typedef struct {
	lv_obj_t *list_panel;
	lv_obj_t *status;
	lv_obj_t *list;
	lv_obj_t *pwd_panel;
	lv_obj_t *pwd_ssid_label;
	lv_obj_t *pwd_ta;
	lv_obj_t *pwd_kb;
	prov_ap_t aps[20];
	uint8_t   ap_count;
	char      selected_ssid[33];
	void    (*back_cb)(void);
	/* cached last connection result — applied immediately on show() */
	bool     result_valid;
	uint8_t  result_status;
	char     result_ssid[33];
	int8_t   result_rssi;
	uint32_t result_ip;
} wifi_provision_t;

void wifi_provision_init(lv_obj_t *parent, wifi_provision_t *w);
void wifi_provision_show(wifi_provision_t *w);
void wifi_provision_hide(wifi_provision_t *w);
void wifi_provision_update(wifi_provision_t *w, const prov_ap_t *aps, uint8_t count);
void wifi_provision_on_result(wifi_provision_t *w, uint8_t status, const char *ssid,
                               int8_t rssi, uint32_t ip);
