GM4AJK/gps-staff/firmware/Nucleo-F767ZI-FreeRTOS/Core/Src/task_ota.c

#include "task_ota.h"
#include "task_sdcard.h"

#include "FreeRTOS.h"
#include "semphr.h"
#include "task.h"
#include "queue.h"
#include "main.h"
#include "rtcm3.h"
#include "ota_tx.h"
#include "sx1262.h"

static rtcm3_t  rtcm3;
static ota_tx_t ota_tx;
static sx1262_t sx1262;

static SemaphoreHandle_t dio1_sem;
QueueHandle_t            uart2_rxq;

void HAL_GPIO_EXTI_Callback(uint16_t gpio_pin)
{
	if (gpio_pin == SX1262_SPI_DIO1_Pin) {
		BaseType_t woken = pdFALSE;
		xSemaphoreGiveFromISR(dio1_sem, &woken);
		portYIELD_FROM_ISR(woken);
	}
}

static void on_rtcm3_frame(const uint8_t *frame, uint16_t len)
{
	ota_tx_push_frame(&ota_tx, frame, len);
	task_sdcard_push_frame(frame, len);
}

static void ota_task(void *arg)
{
	(void)arg;

	sx1262_init(&sx1262, &hspi2,
		SX1262_SPI_CS_GPIO_Port,    SX1262_SPI_CS_Pin,
		SX1262_SPI_RESET_GPIO_Port, SX1262_SPI_RESET_Pin,
		SX1262_SPI_BUSY_GPIO_Port,  SX1262_SPI_BUSY_Pin);

	sx1262_config_gfsk(&sx1262, 434000000UL, 50000, 25000, OTA_TX_PACKET_SIZE, 0);

	ota_tx_init(&ota_tx, &sx1262);
	rtcm3_init(&rtcm3, on_rtcm3_frame);

	__HAL_UART_ENABLE_IT(&huart2, UART_IT_RXNE);

	for (;;) {
		uint8_t b;
		if (xQueueReceive(uart2_rxq, &b, pdMS_TO_TICKS(1)) == pdTRUE) {
			rtcm3_process_byte(&rtcm3, b);
			while (xQueueReceive(uart2_rxq, &b, 0) == pdTRUE)
				rtcm3_process_byte(&rtcm3, b);
		}
		rtcm3_loop(&rtcm3);
		if (xSemaphoreTake(dio1_sem, 0) == pdTRUE)
			sx1262_service_tx(&sx1262);
	}
}

void task_ota_init(void)
{
	dio1_sem  = xSemaphoreCreateBinary();
	uart2_rxq = xQueueCreate(256, sizeof(uint8_t));
	configASSERT(dio1_sem);
	configASSERT(uart2_rxq);
	xTaskCreate(ota_task, "ota", 512, NULL, tskIDLE_PRIORITY + 2, NULL);
}
