GM4AJK/gps-staff/firmware/Nucleo-F767ZI/Core/Inc/app.h

#ifndef INC_APP_H_
#define INC_APP_H_

#include "rtcm3.h"

extern rtcm3_t rtcm3;

void app_init(void);
void app_loop(void);
void app_1ms(void);
void app_log(const char *fmt, ...);

#endif /* INC_APP_H_ */
