GM4AJK/gps-staff/firmware/Nucleo-G431-Fake-F9P/Core/Inc/flags.h

/*
 * Author: Andy Kirkham
 */

#ifndef INC_FLAGS_H_
#define INC_FLAGS_H_

#include <stdbool.h>

#define MAKE_H(suffix) \
	bool flag_set_##suffix(void); \
	bool flag_get_##suffix(void); \
	bool flag_peek_##suffix(void);

MAKE_H(100MS)
MAKE_H(1000MS)

#endif /* INC_FLAGS_H_ */
