GM4AJK/gps-staff/firmware/Nucleo-G431-Fake-F9P/Core/Src/rtcm_sample.c

#include "rtcm_sample.h"

const uint8_t rtcm_sample_data[6384] = {
	0xD3, 0x00, 0x13, 0x3E, 0xD0, 0x00, 0x03, 0x09, 0x1E, 0xA3, 0xB5, 0xF6,
	0xBF, 0xFE, 0x01, 0x0F, 0x9A, 0x0B, 0xAE, 0x60, 0xD1, 0x72, 0x10, 0xDD,
	0x57, 0xD3, 0x00, 0x72, 0x43, 0x20, 0x00, 0x25, 0xC1, 0x48, 0x7E, 0x00,
	0x00, 0x05, 0x03, 0x2F, 0x82, 0x00, 0x00, 0x00, 0x00, 0x20, 0x00, 0x00,
	0x00, 0x7F, 0xF4, 0x65, 0x34, 0x74, 0x64, 0xF4, 0x34, 0xB4, 0x85, 0x25,
	0x04, 0x8D, 0x2C, 0x1F, 0x40, 0x42, 0x69, 0xFF, 0x4A, 0x5E, 0xE9, 0x13,
	0x0D, 0x69, 0x00, 0xBF, 0x13, 0x7E, 0x00, 0x16, 0x41, 0xDD, 0x7C, 0xA2,
	0x8E, 0xC5, 0x03, 0xEC, 0x9A, 0x4F, 0xBC, 0xF6, 0x19, 0xEE, 0xE6, 0xFD,
	0xFB, 0x71, 0xDF, 0xF8, 0x01, 0x20, 0xA2, 0xBE, 0xFE, 0xBD, 0x8A, 0x13,
	0x1A, 0xCF, 0xA2, 0xE3, 0x61, 0xF5, 0x2E, 0xFA, 0x8A, 0x37, 0xFB, 0x7C,
	0x10, 0x5F, 0xF2, 0xBF, 0x43, 0xA5, 0xFC, 0x7F, 0xFF, 0xFF, 0xDF, 0xF8,
	0x00, 0xC1, 0xBB, 0xAB, 0x7E, 0xCB, 0xAD, 0x6E, 0x3B, 0x40, 0x0B, 0x2C,
	0xE4, 0xD3, 0x00, 0x3F, 0x43, 0xC0, 0x00, 0x33, 0xB9, 0xED, 0x3C, 0x00,
	0x00, 0x06, 0x03, 0x80, 0x00, 0x00, 0x00, 0x00, 0x00, 0x20, 0x00, 0x00,
	0x00, 0x7D, 0x01, 0x15, 0x19, 0x01, 0x28, 0x04, 0x7A, 0x0E, 0x1D, 0x19,
	0xAC, 0xC2, 0xED, 0xFF, 0x6F, 0x98, 0xC7, 0x4D, 0x9F, 0x0F, 0x9D, 0xA1,
	0x33, 0x7F, 0x8B, 0x31, 0xEB, 0x24, 0xE7, 0xD7, 0x9F, 0x9F, 0x8C, 0x30,
	0x7F, 0xFF, 0xF8, 0x2E, 0x9A, 0x9B, 0xF2, 0xD8, 0xA0, 0x19, 0xD3, 0x01,
	0x26, 0x44, 0x60, 0x00, 0x00, 0x00, 0x00, 0x00, 0x00, 0x00, 0x00, 0x00,
	0x00, 0x00, 0x00, 0x00, 0x00, 0x00, 0x00, 0x00, 0x00, 0x00, 0x00, 0x00,
	0x00, 0x00, 0x00, 0x00, 0x00, 0x00, 0x00, 0x00, 0x00, 0x00, 0x00, 0x00,
	0x00, 0x00, 0x00, 0x00, 0x00, 0x00, 0x00, 0x00, 0x00, 0x00, 0x00, 0x00,
	0x00, 0x00, 0x00, 0x00, 0x00, 0x00, 0x00, 0x00, 0x00, 0x00, 0x00, 0x00,
	0x00, 0x00, 0x00, 0x00, 0x00, 0x00, 0x00, 0x00, 0x00, 0x00, 0x00, 0x00,
	0x00, 0x00, 0x00, 0x00, 0x00, 0x00, 0x00, 0x00, 0x00, 0x00, 0x00, 0x00,
	0x00, 0x00, 0x00, 0x00, 0x00, 0x00, 0x00, 0x00, 0x00, 0x00, 0x00, 0x00,
	0x00, 0x00, 0x00, 0x00, 0x00, 0x00, 0x00, 0x00, 0x00, 0x00, 0x00, 0x00,
	0x00, 0x00, 0x00, 0x00, 0x00, 0x00, 0x00, 0x00, 0x00, 0x00, 0x00, 0x00,
	0x00, 0x00, 0x00, 0x00, 0x00, 0x00, 0x00, 0x00, 0x00, 0x00, 0x00, 0x00,
	0x00, 0x00, 0x00, 0x00, 0x00, 0x00, 0x00, 0x00, 0x00, 0x00, 0x00, 0x00,
	0x00, 0x00, 0x00, 0x00, 0x00, 0x00, 0x00, 0x00, 0x00, 0x00, 0x00, 0x00,
	0x00, 0x00, 0x00, 0x00, 0x00, 0x00, 0x00, 0x00, 0x00, 0x00, 0x00, 0x00,
	0x00, 0x00, 0x00, 0x00, 0x00, 0x00, 0x00, 0x00, 0x00, 0x00, 0x00, 0x00,
	0x00, 0x00, 0x00, 0x00, 0x00, 0x00, 0x00, 0x00, 0x00, 0x00, 0x00, 0x00,
	0x00, 0x00, 0x00, 0x00, 0x00, 0x00, 0x00, 0x00, 0x00, 0x00, 0x00, 0x00,
	0x00, 0x00, 0x00, 0x00, 0x00, 0x00, 0x00, 0x00, 0x00, 0x00, 0x00, 0x00,
	0x00, 0x00, 0x00, 0x00, 0x00, 0x00, 0x00, 0x00, 0x00, 0x00, 0x00, 0x00,
	0x00, 0x00, 0x00, 0x00, 0x00, 0x00, 0x00, 0x00, 0x00, 0x00, 0x00, 0x00,
	0x00, 0x00, 0x00, 0x00, 0x00, 0x00, 0x00, 0x00, 0x00, 0x00, 0x00, 0x00,
	0x00, 0x00, 0x00, 0x00, 0x00, 0x00, 0x00, 0x00, 0x00, 0x00, 0x00, 0x00,
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
};

const uint32_t rtcm_sample_len = 6384;

const uint32_t rtcm_sample_cycle_offsets[6] = {
	0, 1064, 2128, 3192, 4256, 5320
};

const uint32_t rtcm_sample_cycle_count = 6;
